prittt/CO2-HopCannon/imgs/photos/preview_00.jpg

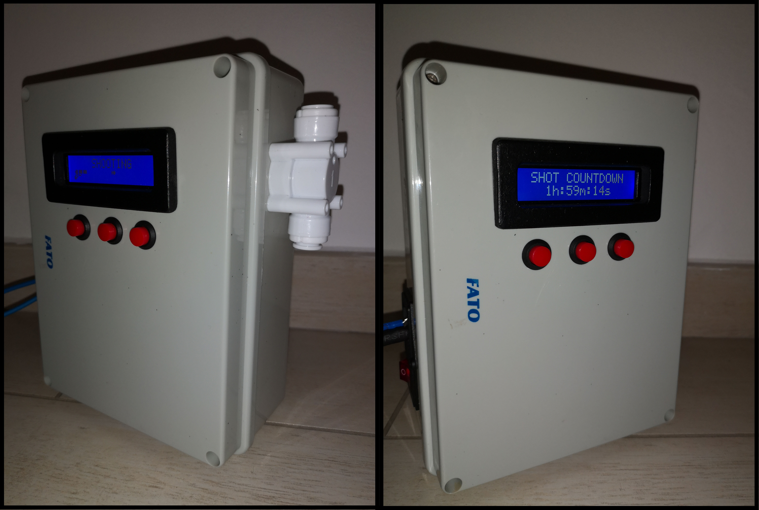
imgs/photos/preview_00.jpg
