prittt/CO2-HopCannon/pcb/export/pdf/CO2  HopCannon_etch_silk_bottom.pdf

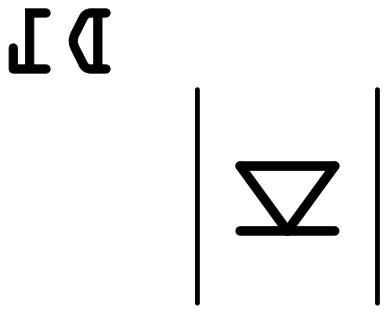
[picture p53: page 1]
