prittt/CO2-HopCannon/pcb/export/pdf/CO2  HopCannon_etch_silk_bottom_mirror.pdf

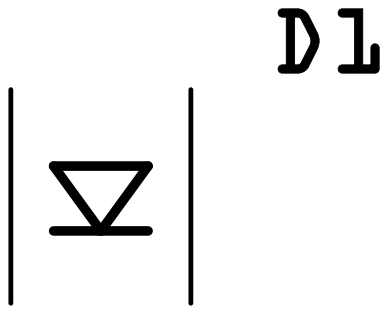
[picture p54: page 1]
