prittt/CO2-HopCannon/pcb/export/pdf/CO2  HopCannon_etch_silk_top.pdf

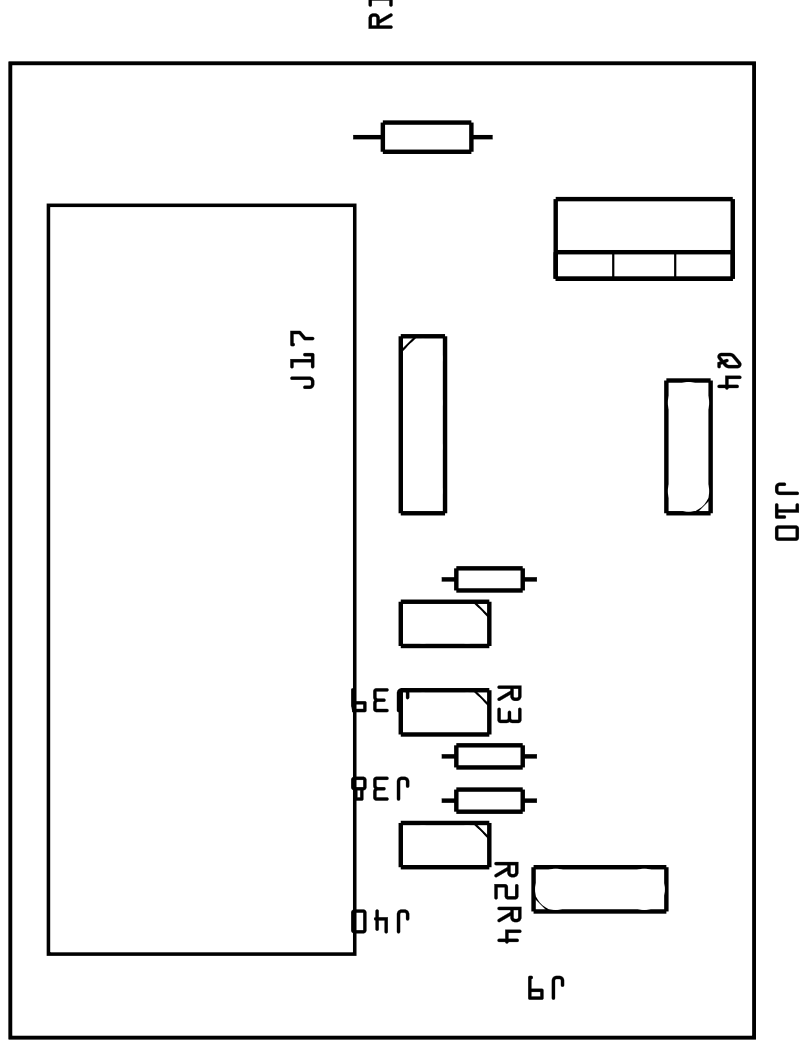
[picture p55: page 1]
