prittt/CO2-HopCannon/pcb/export/pdf/CO2  HopCannon_etch_silk_top_mirror.pdf

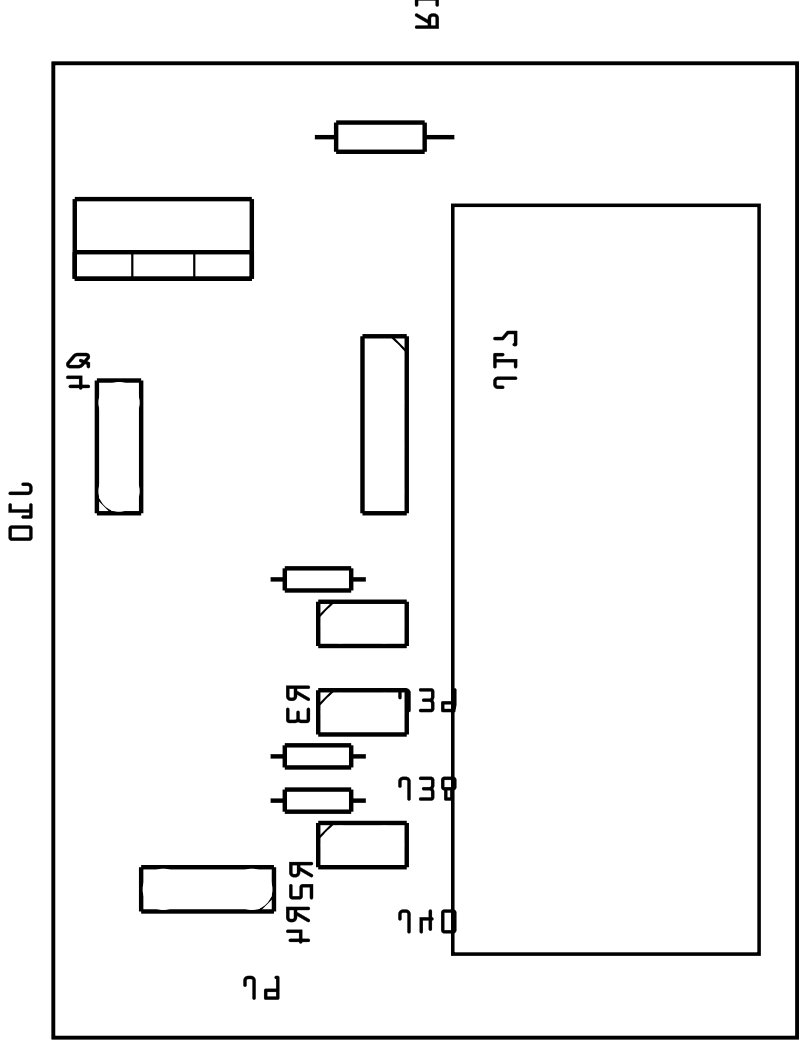
[picture p56: page 1]
