prittt/CO2-HopCannon/CO2-HopCannon/nano_pins.h

#ifndef CO2_HOPCANNON_NANO_PINS_H_
#define CO2_HOPCANNON_NANO_PINS_H_

//************************************************************
// BUTTONs
//************************************************************

#define BTN_S A1 // Setup
#define BTN_P A2 // Plus 
#define BTN_M A3 // Minus

//************************************************************
// SOLENOID
//************************************************************

#define SOLENOID 2 // D2

//************************************************************
// LCD SCREEN
//************************************************************

#define SDA A4 
#define SCL A5 

#endif // CO2_HOPCANNON_NANO_PINS_H_
